Rhettus/Saturn6/Panels/side_panel-top.stl

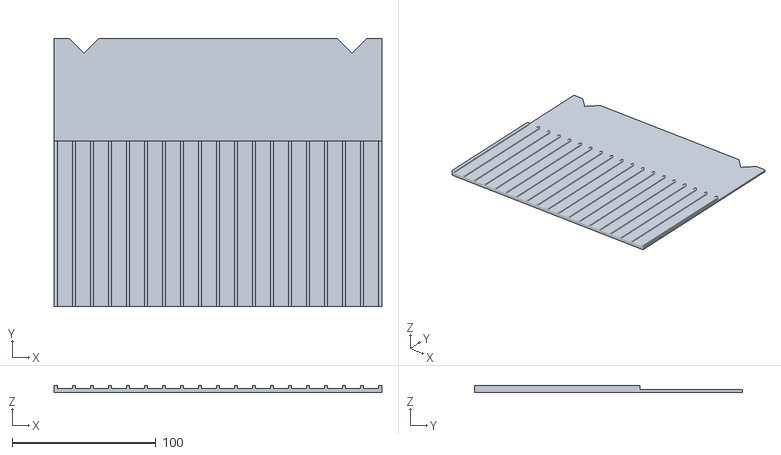
[picture p15: CAD file, 2024-12-31]
Panels/side_panel-top.stl
228.0 x 186.4 x 5.00
