Rhettus/Saturn6/Chassis/Blank-Saturn6.stl

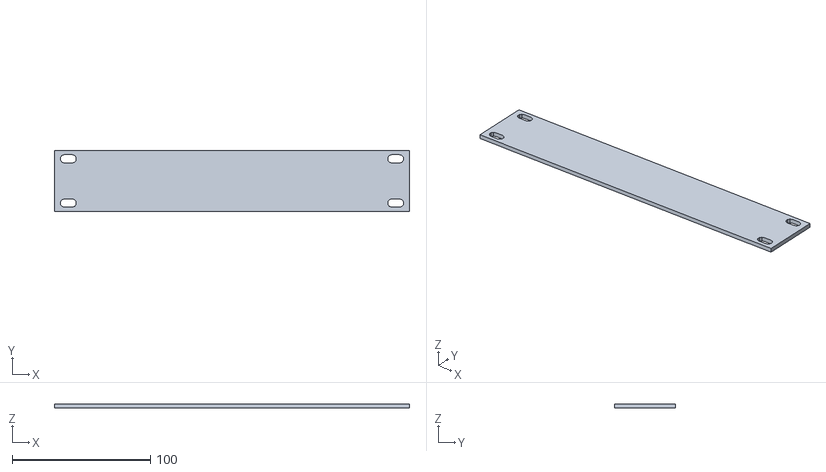
[picture p16: CAD file, 2024-12-31]
Chassis/Blank-Saturn6.stl
257.0 x 44.1 x 3.00
