Rhettus/Saturn6/Face Plates/fw-faceplate.stl

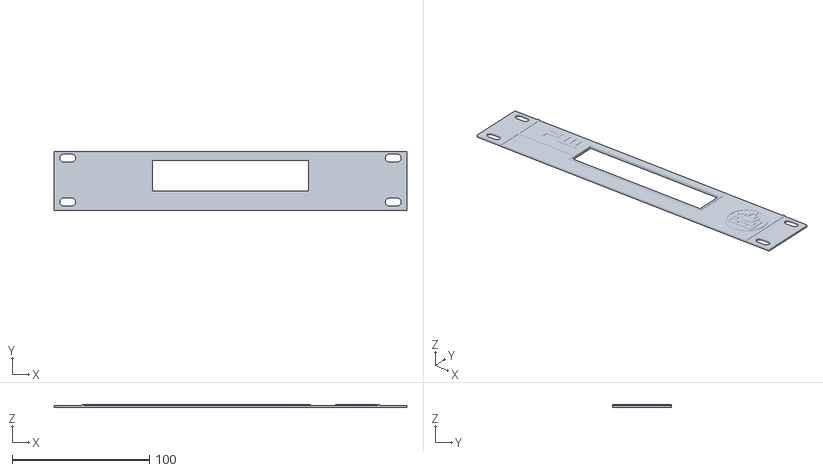
[picture p17: CAD file, 2024-12-31]
Face Plates/fw-faceplate.stl
257.0 x 42.8 x 2.10
