Rhettus/Saturn6/Other/Latch M3x8.stl

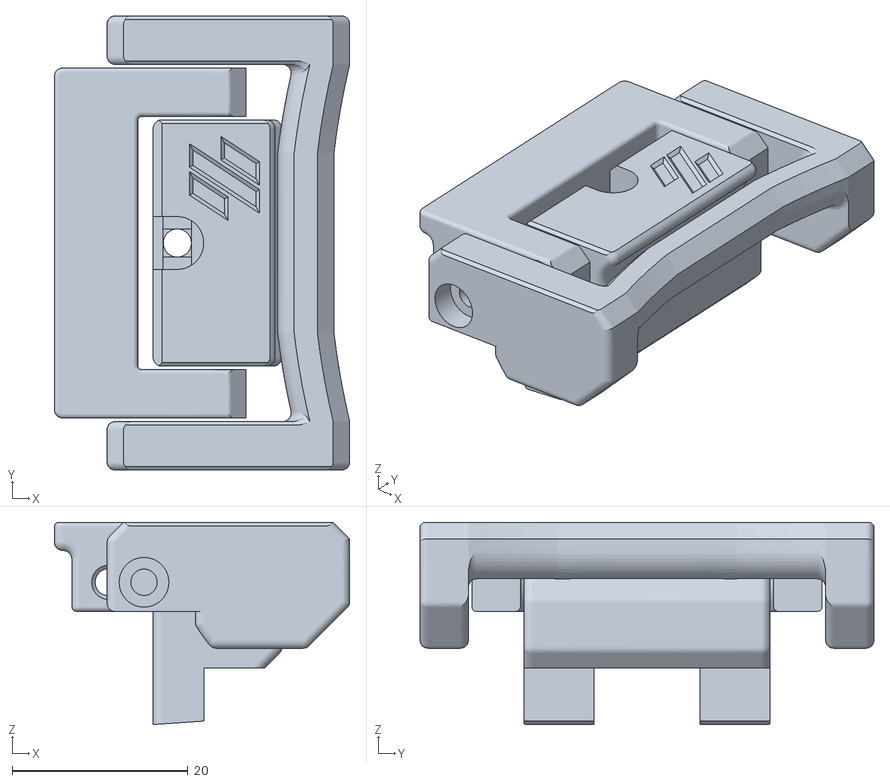
[picture p18: CAD file, 2024-12-31]
Other/Latch M3x8.stl
33.6 x 51.6 x 23.0
