Rhettus/Saturn6/Panels/side_panel-middle.stl

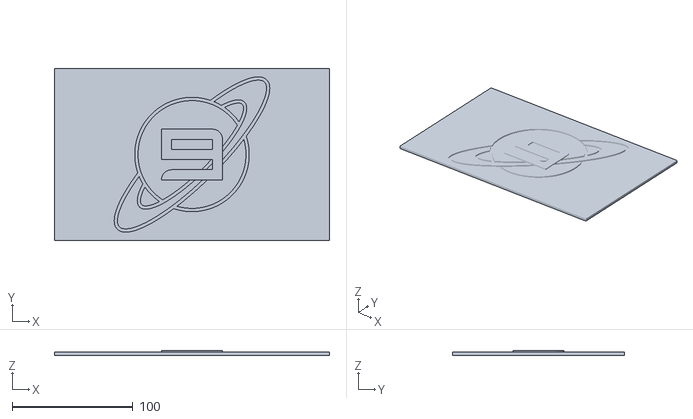
[picture p19: CAD file, 2024-12-31]
Panels/side_panel-middle.stl
228.0 x 143.0 x 4.00
