Rhettus/Saturn6/Face Plates/sw2-faceplate.stl

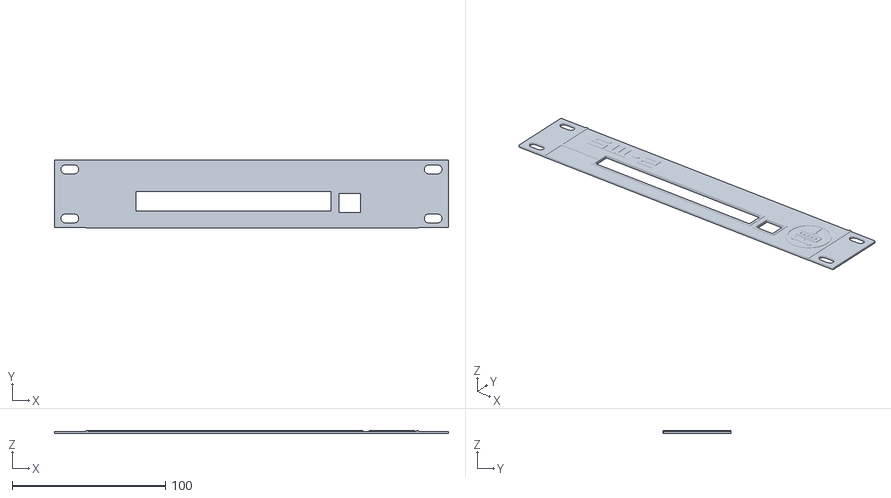
[picture p20: CAD file, 2024-12-31]
Face Plates/sw2-faceplate.stl
257.0 x 44.1 x 2.10
