Rhettus/Saturn6/Other/158MM SKIRT.stl

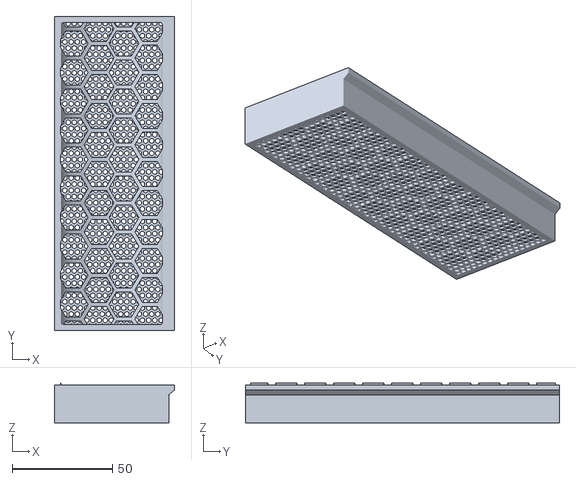
[picture p21: CAD file, 2024-12-31]
Other/158MM SKIRT.stl
60.0 x 157.0 x 19.8
