Rhettus/Saturn6/Panels/side_panel-bottom.stl

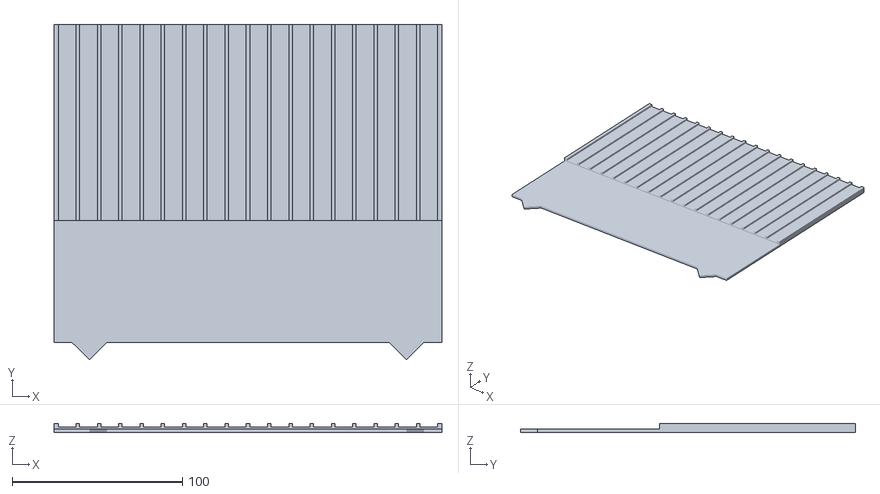
[picture p22: CAD file, 2024-12-31]
Panels/side_panel-bottom.stl
228.0 x 197.0 x 5.00
