Rhettus/Saturn6/Chassis/fw-unifi-usg.stl

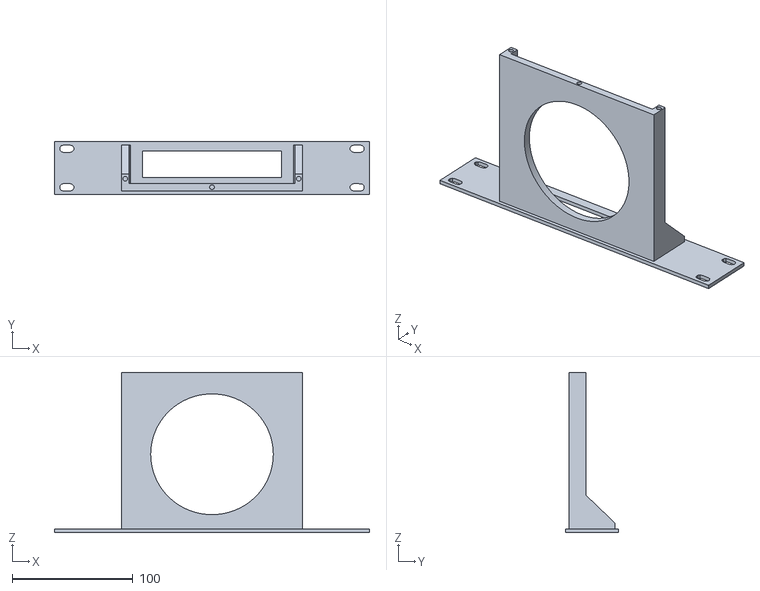
[picture p23: CAD file, 2024-12-31]
Chassis/fw-unifi-usg.stl
261.0 x 44.1 x 132.6
