Rhettus/Saturn6/Other/Top Panel Corner Bracket.3mf

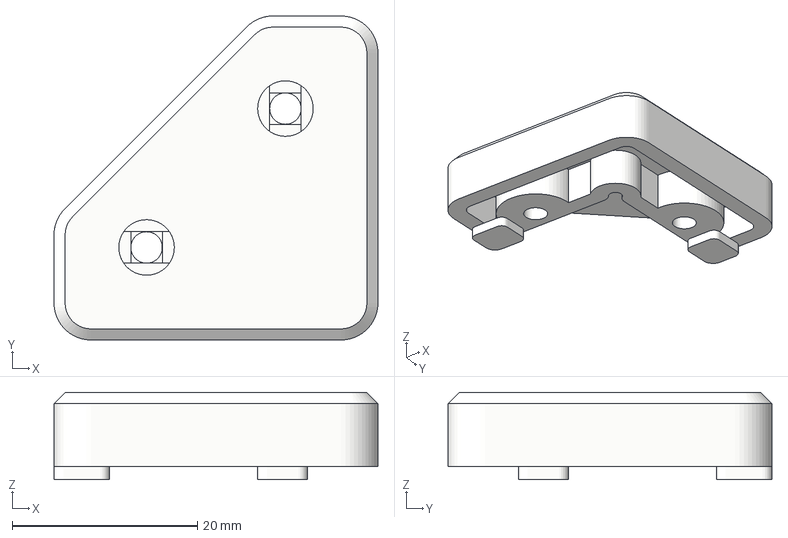
[picture p24: CAD file, 2024-12-31]
Other/Top Panel Corner Bracket.3mf
35.0 x 35.0 x 9.40 mm
