Rhettus/Saturn6/Panels/Top Unifi Lite 6.stl

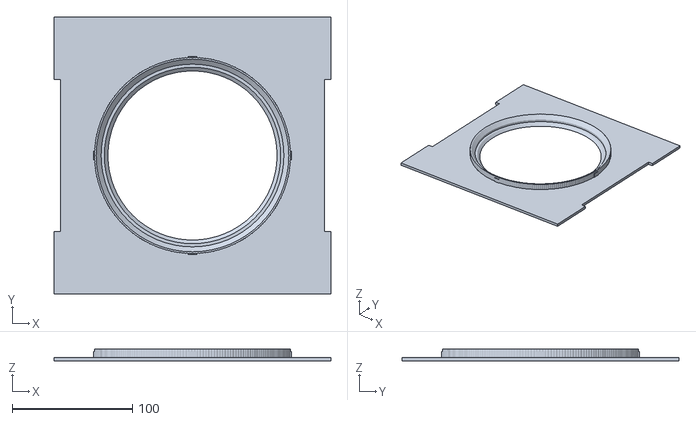
[picture p25: CAD file, 2024-12-31]
Panels/Top Unifi Lite 6.stl
230.0 x 230.0 x 9.76
