Rhettus/Saturn6/Chassis/patchpanel-keystone.stl

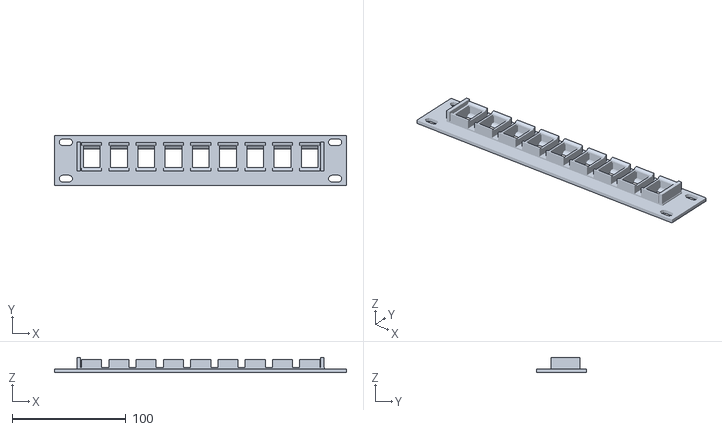
[picture p26: CAD file, 2024-12-31]
Chassis/patchpanel-keystone.stl
257.0 x 44.1 x 13.0
