Rhettus/Saturn6/Chassis/nas-cm3588.stl

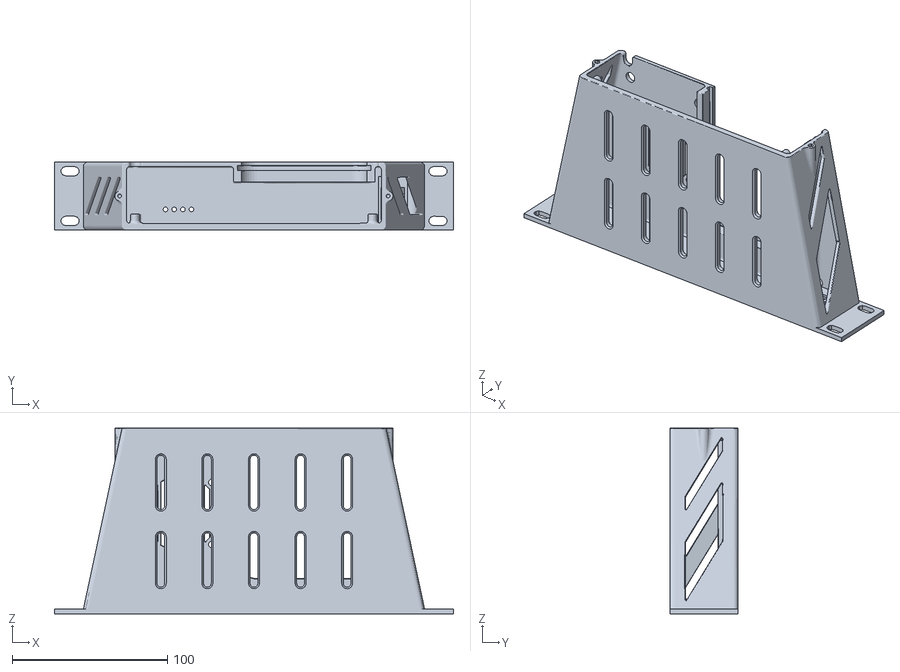
[picture p27: CAD file, 2024-12-31]
Chassis/nas-cm3588.stl
257.0 x 44.1 x 119.7
