Rhettus/Saturn6/Face Plates/Saturn6-faceplate.stl

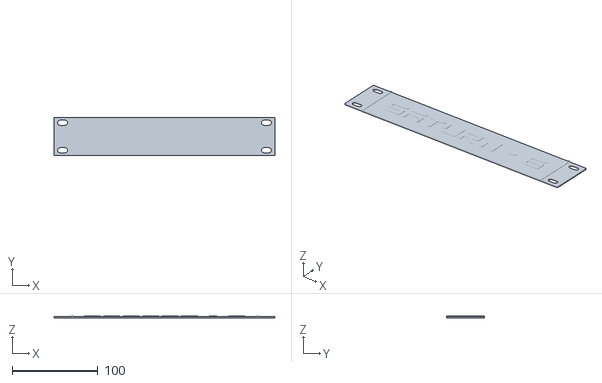
[picture p28: CAD file, 2024-12-31]
Face Plates/Saturn6-faceplate.stl
257.0 x 44.1 x 2.10
