Rhettus/Saturn6/Chassis/switch-chassis.stl

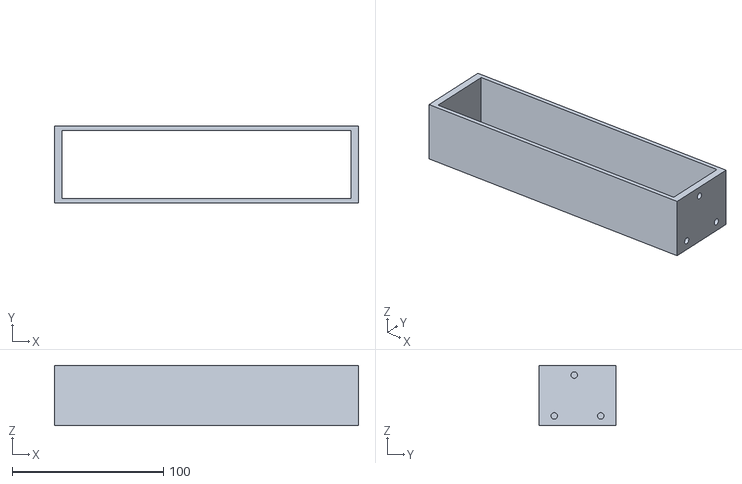
[picture p29: CAD file, 2024-12-31]
Chassis/switch-chassis.stl
201.0 x 50.7 x 40.0
