Rhettus/Saturn6/Chassis/switch-ears.stl

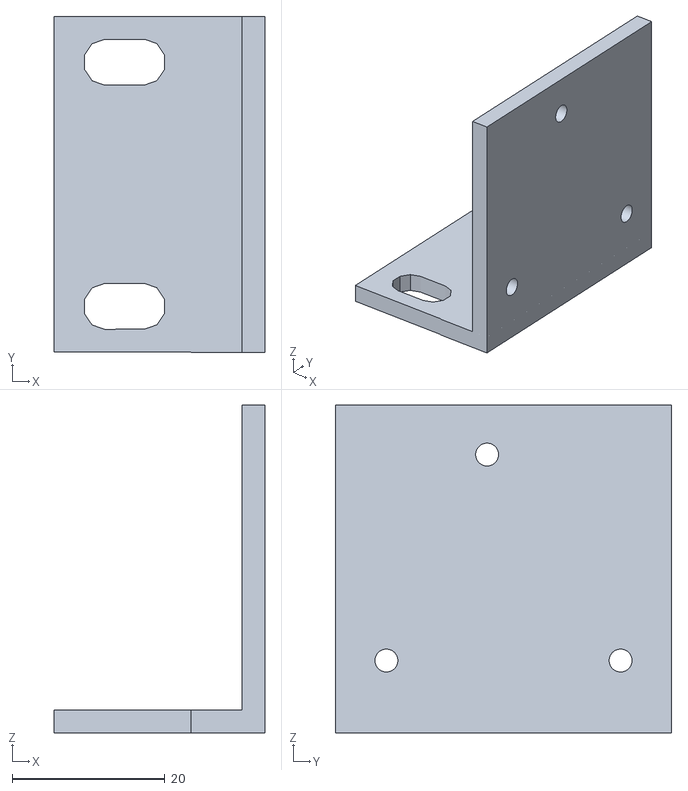
[picture p30: CAD file, 2024-12-31]
Chassis/switch-ears.stl
27.6 x 44.1 x 43.0
