Rhettus/Saturn6/Face Plates/RPi_Cluster-faceplate.stl

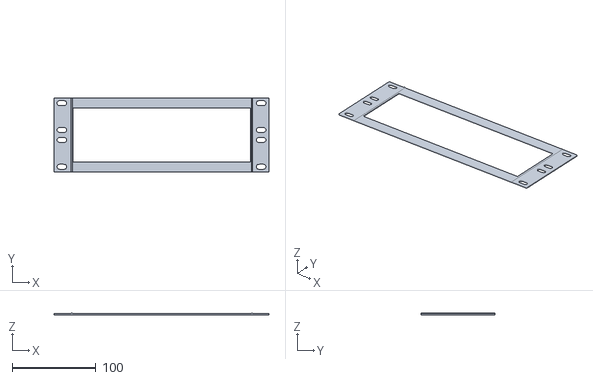
[picture p31: CAD file, 2024-12-31]
Face Plates/RPi_Cluster-faceplate.stl
257.0 x 88.1 x 2.10
